jalexandre0/saci-temperature-controller/src/DS18B20.h

#ifndef DS18B20_H
#define DS18B20_H

#include <OneWire.h>
#include <DallasTemperature.h>

extern OneWire  pin;
extern DallasTemperature tempSensor ;

float beerTemp() ;
float fridgeTemp() ;
void sensorInit() ;
void sensorRequest() ;
static float _beerTemp ;
static float _fridgeTemp ;
#endif
